cross-bound/PurplePDK/IMG/PCB_back.jpg

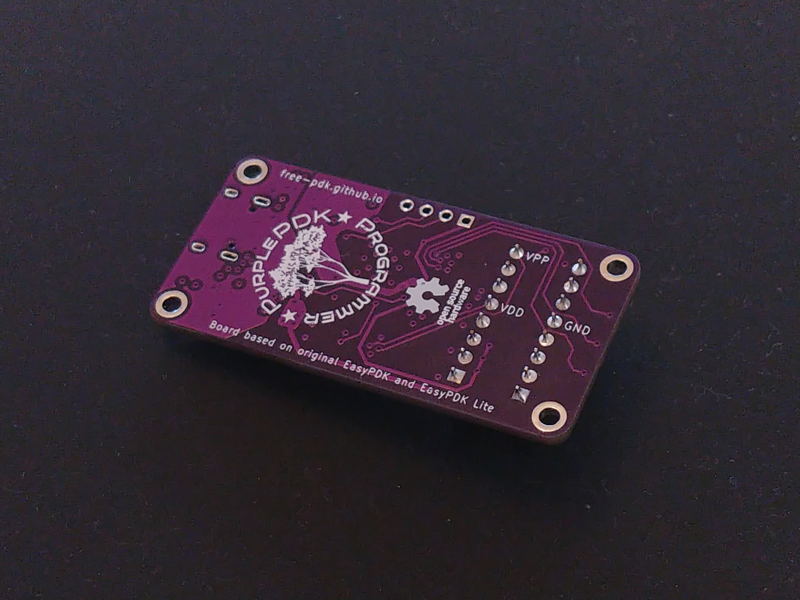
IMG/PCB_back.jpg
